dubicube/minitel2.0/mecanic/keyboard_connector/photo0.jpg

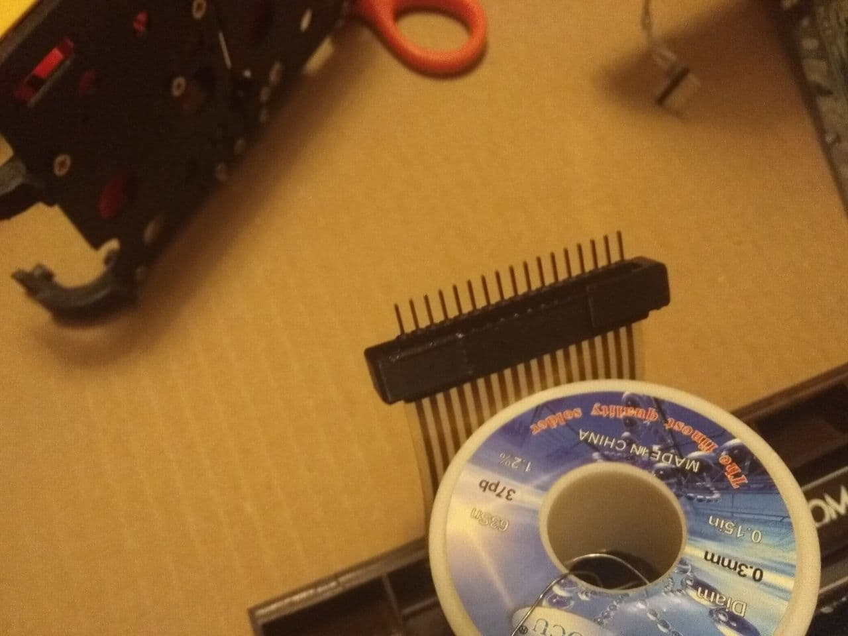
mecanic/keyboard_connector/photo0.jpg
