dubicube/minitel2.0/mecanic/keyboard_connector/photo1.jpg

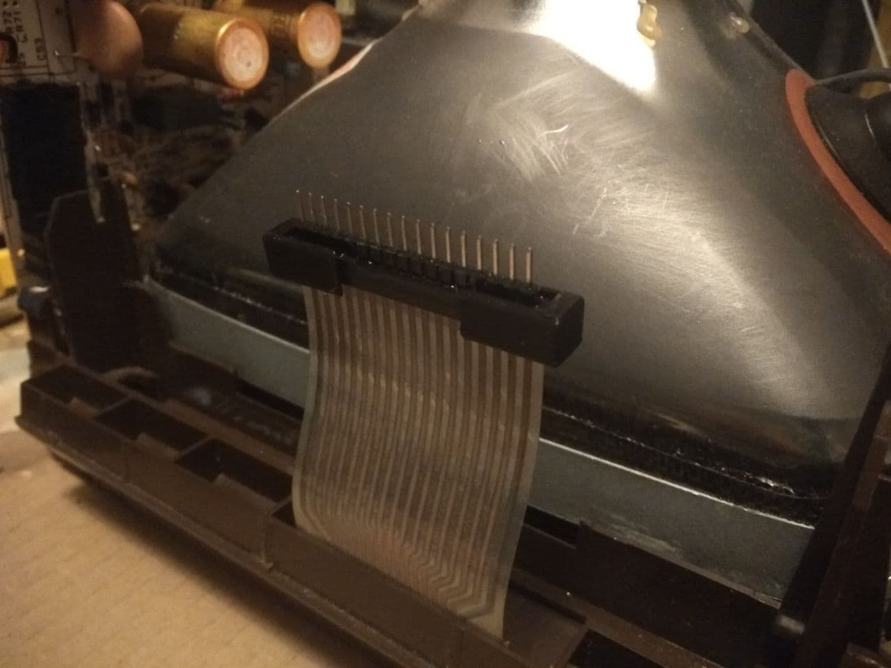
mecanic/keyboard_connector/photo1.jpg
